madelinegannon/drawing_with_machines/samples/tiliing/truchet/truchet_multiscale_gh_def.png

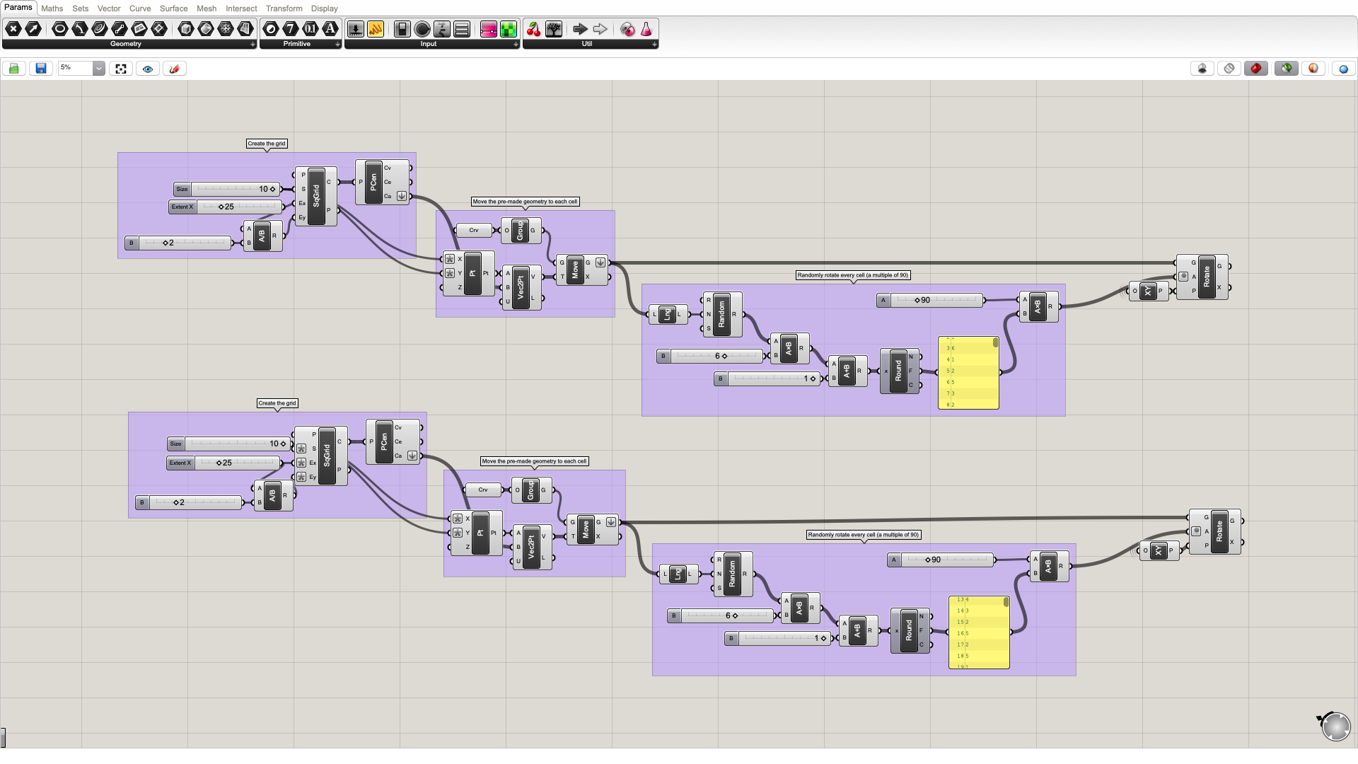
samples/tiliing/truchet/truchet_multiscale_gh_def.png
